nfelber/IMU-Motion-Tracking-Glove/src/mtg-flappy_bird/img/background.jpg

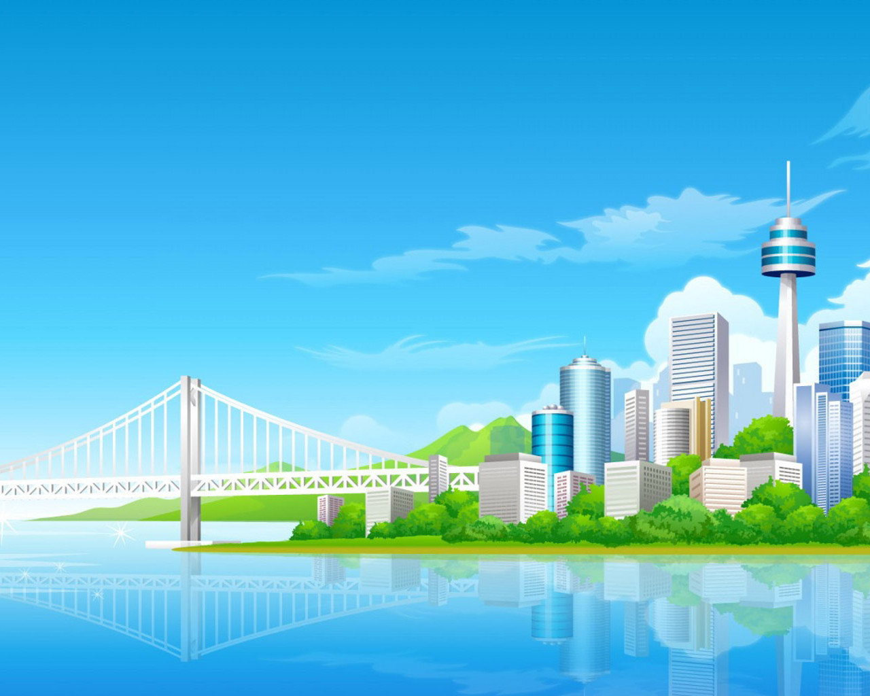
src/mtg-flappy_bird/img/background.jpg
