nfelber/IMU-Motion-Tracking-Glove/src/mtg-flappy_bird/img/background_event.jpg

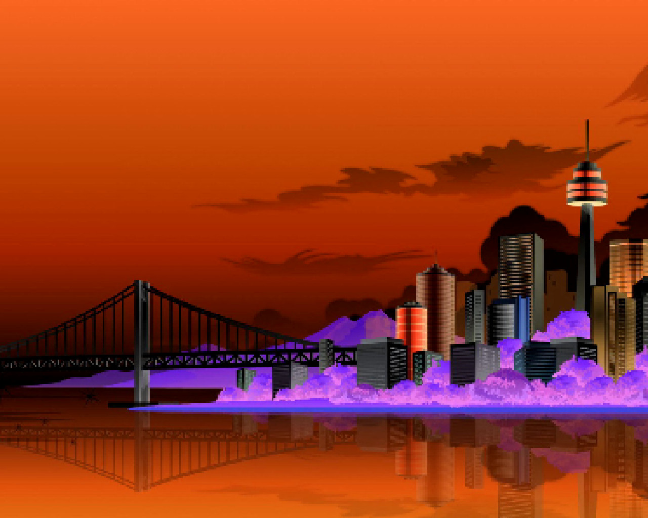
src/mtg-flappy_bird/img/background_event.jpg
