nfelber/IMU-Motion-Tracking-Glove/src/mtg-flappy_bird/img/floor.png

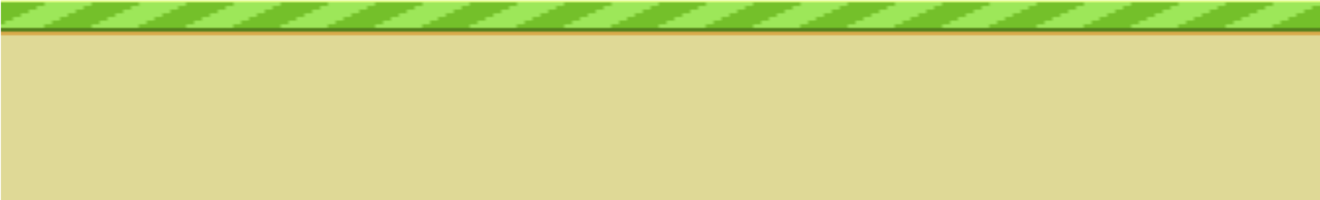
src/mtg-flappy_bird/img/floor.png
