nfelber/IMU-Motion-Tracking-Glove/src/mtg-flappy_bird/img/game_over.png

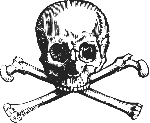
src/mtg-flappy_bird/img/game_over.png
