nfelber/IMU-Motion-Tracking-Glove/src/mtg-flappy_bird/img/restart.png

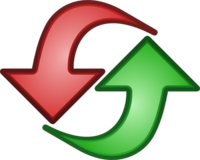
src/mtg-flappy_bird/img/restart.png
